MarcoBraun84/OsPi-Pico/Fusion 360/Elektronik Libs/LM27762DSST.stp

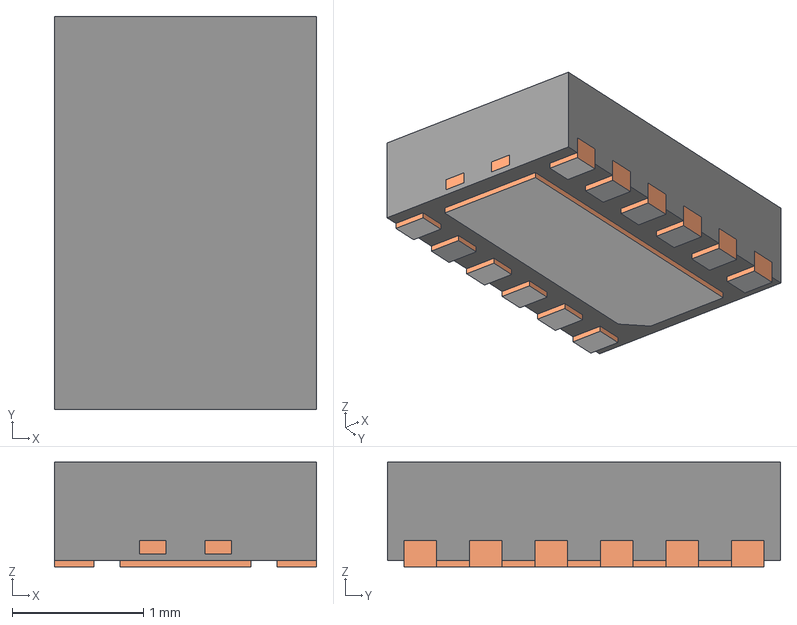
[picture p35: CAD file, 2024-03-17]
Fusion 360/Elektronik Libs/LM27762DSST.stp
2.00 x 3.00 x 0.8 mm
BODY-SON
FRAME-DSS0012B
PIN1-ID
