MarcoBraun84/OsPi-Pico/Fusion 360/Elektronik Libs/73137-5003.stp

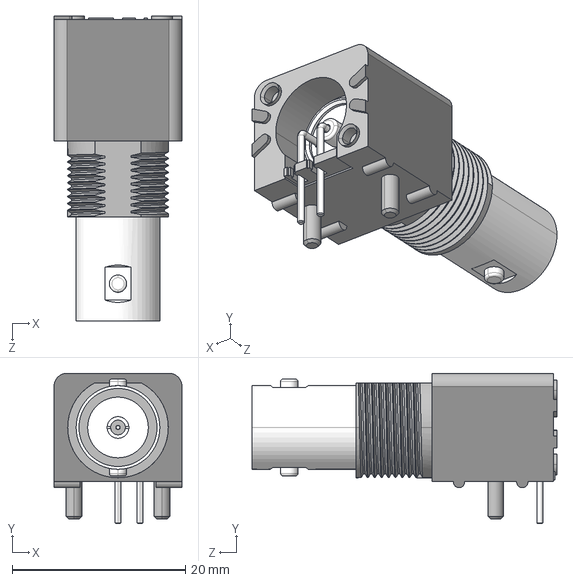
[picture p36: CAD file, 2024-03-17]
Fusion 360/Elektronik Libs/73137-5003.stp
14.8 x 17.4 x 35.2 mm
